hannahstratfull/physiological-monitoring/CAD/handheld device/!!__83.SLDPRT

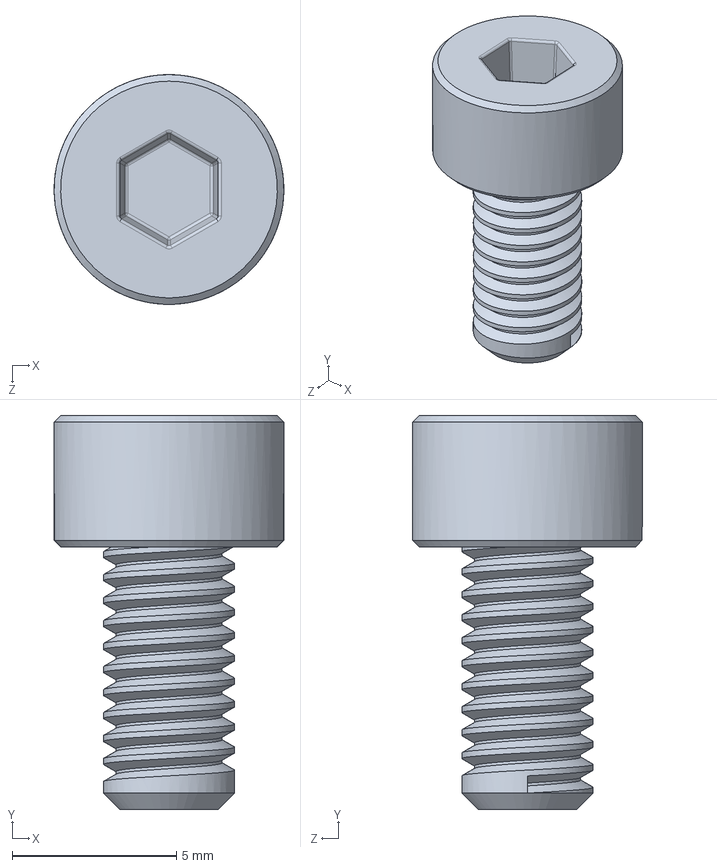
[picture p15: CAD file, 2022-05-07]
CAD/handheld device/!!__83.SLDPRT
7.00 x 12.0 x 7.00 mm
