hannahstratfull/physiological-monitoring/CAD/LCD/Back Plate.SLDPRT

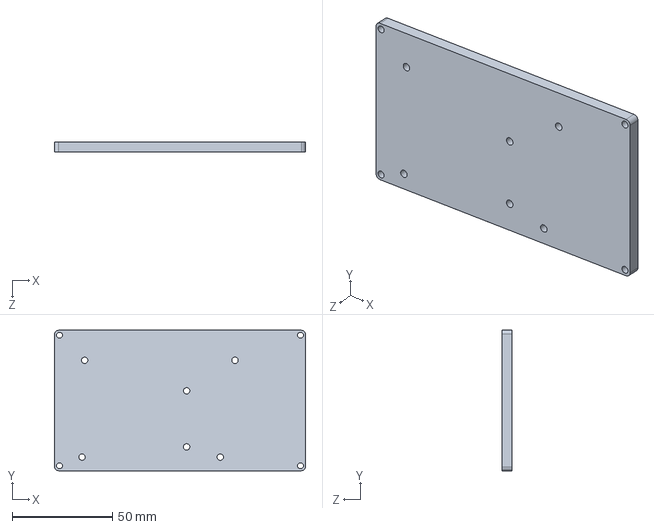
[picture p16: CAD file, 2022-05-07]
CAD/LCD/Back Plate.SLDPRT
125.0 x 70.0 x 5.00 mm
