hannahstratfull/physiological-monitoring/CAD/microphone/Name tag.SLDPRT

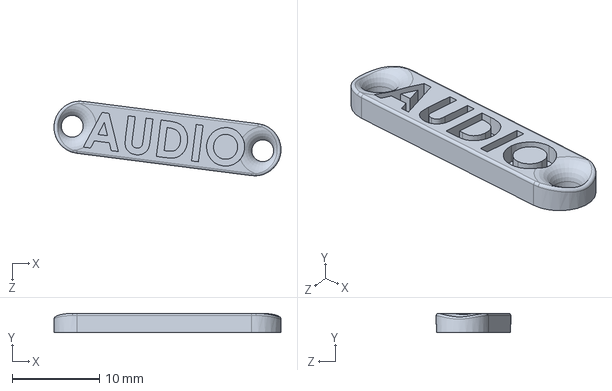
[picture p17: CAD file, 2022-05-07]
CAD/microphone/Name tag.SLDPRT
26.0 x 2.20 x 8.56 mm
