hannahstratfull/physiological-monitoring/CAD/ECG/ECG module.SLDPRT

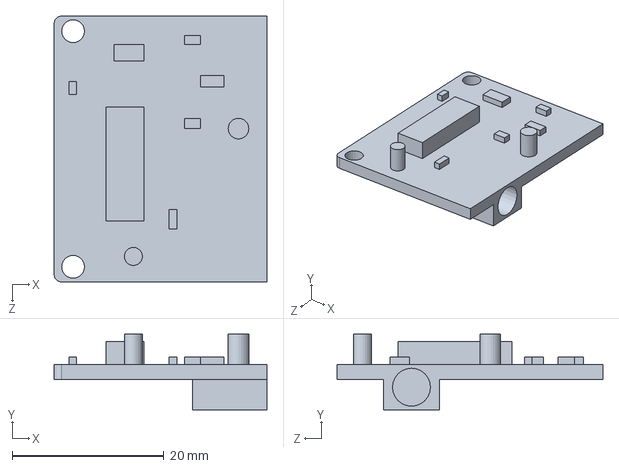
[picture p18: CAD file, 2022-05-07]
CAD/ECG/ECG module.SLDPRT
28.0 x 10.0 x 35.0 mm
