hannahstratfull/physiological-monitoring/CAD/EMG/Name tag.SLDPRT

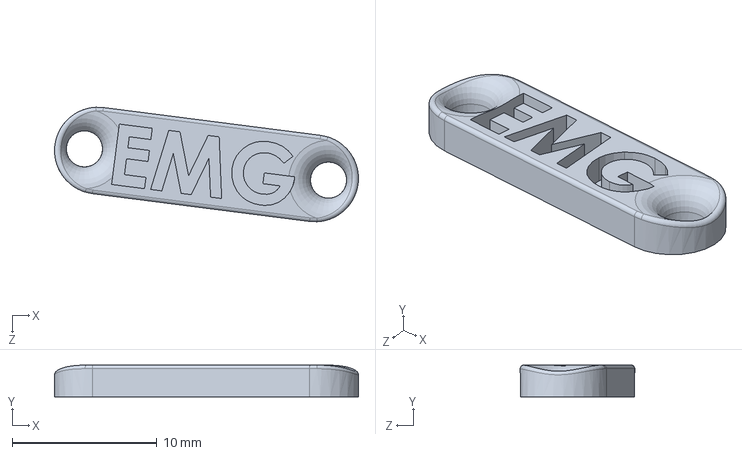
[picture p19: CAD file, 2022-05-07]
CAD/EMG/Name tag.SLDPRT
21.0 x 2.20 x 7.91 mm
