hannahstratfull/physiological-monitoring/CAD/LCD/LED 5mm.SLDPRT

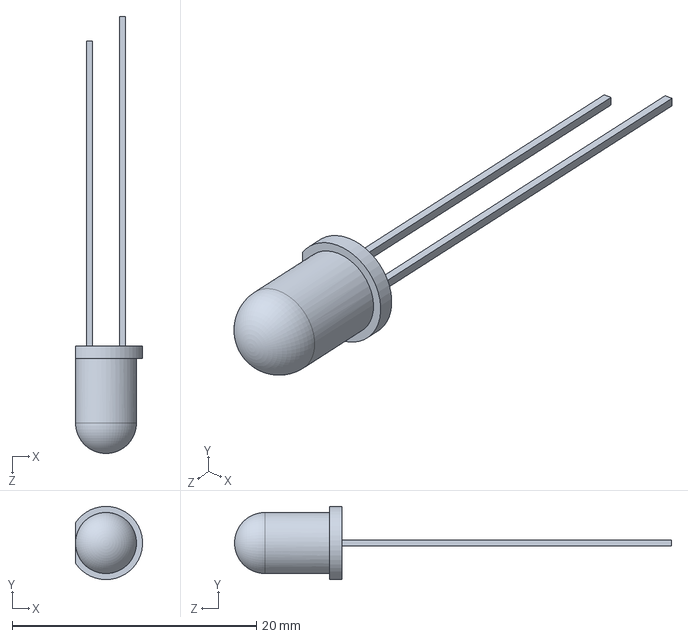
[picture p20: CAD file, 2022-05-07]
CAD/LCD/LED 5mm.SLDPRT
5.49 x 6.00 x 35.8 mm
