hannahstratfull/physiological-monitoring/CAD/microphone/Microphone Lid.SLDPRT

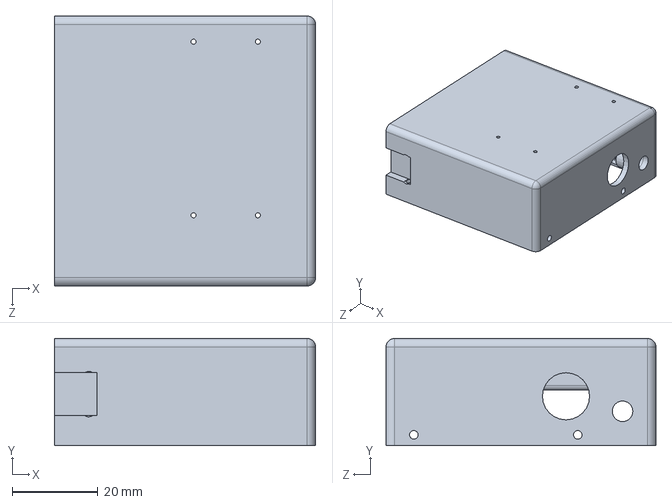
[picture p21: CAD file, 2022-05-07]
CAD/microphone/Microphone Lid.SLDPRT
61.0 x 25.0 x 63.0 mm
