hannahstratfull/physiological-monitoring/CAD/ECG/ECG Box Lid.SLDPRT

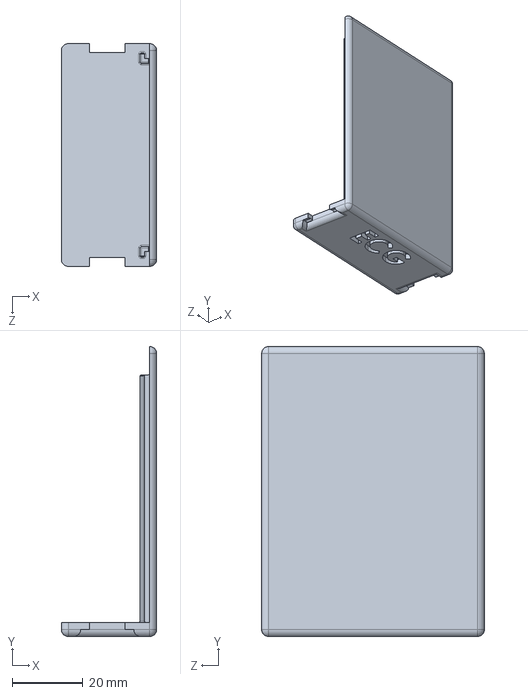
[picture p22: CAD file, 2022-05-07]
CAD/ECG/ECG Box Lid.SLDPRT
27.0 x 82.0 x 63.0 mm
