hannahstratfull/physiological-monitoring/CAD/EMG/EMG box.SLDPRT

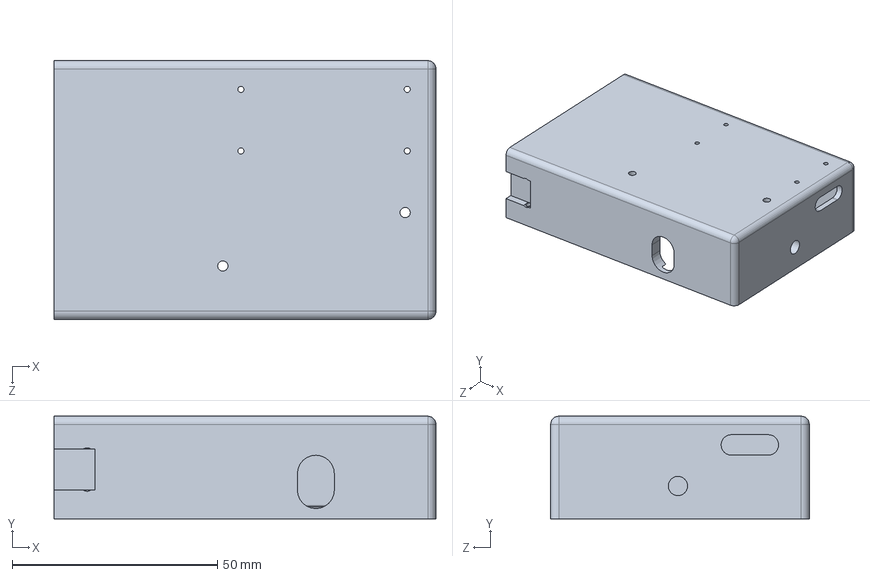
[picture p23: CAD file, 2022-05-07]
CAD/EMG/EMG box.SLDPRT
93.0 x 25.0 x 63.0 mm
