hannahstratfull/physiological-monitoring/CAD/Flexiforce/Flexiforce cable holder.SLDPRT

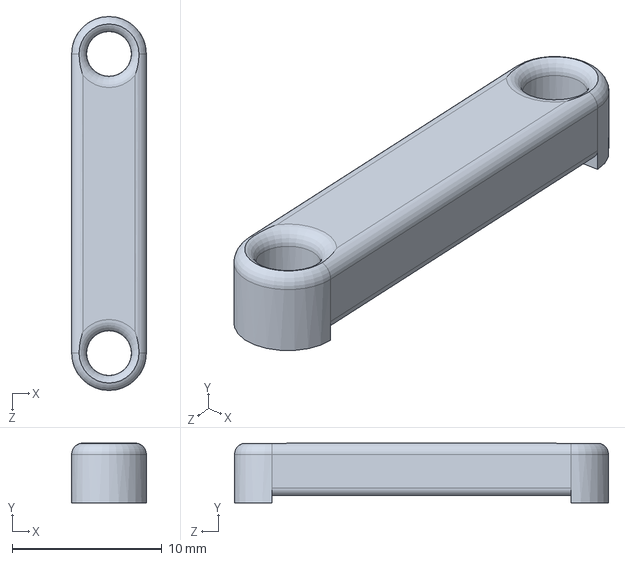
[picture p24: CAD file, 2022-05-07]
CAD/Flexiforce/Flexiforce cable holder.SLDPRT
5.00 x 4.00 x 25.0 mm
