hannahstratfull/physiological-monitoring/CAD/ECG/Name tag.SLDPRT

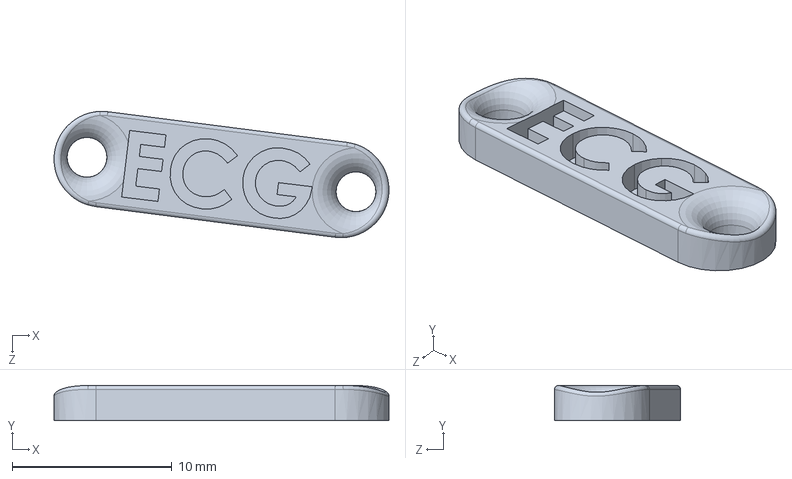
[picture p25: CAD file, 2022-05-07]
CAD/ECG/Name tag.SLDPRT
21.0 x 2.20 x 7.91 mm
