hannahstratfull/physiological-monitoring/CAD/Flexiforce/button top.SLDPRT

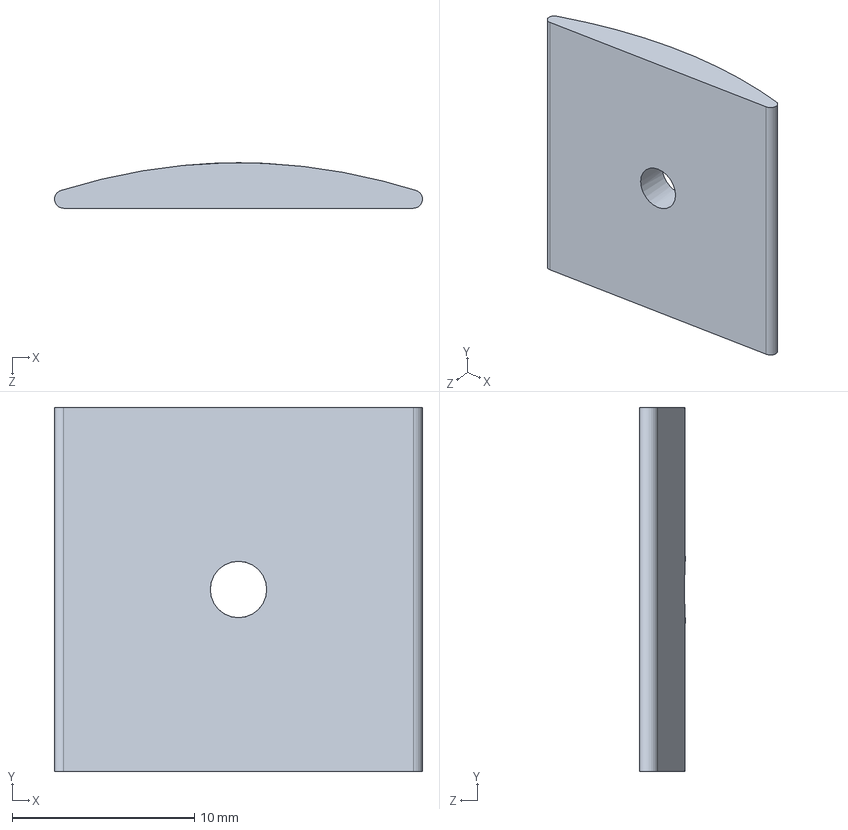
[picture p26: CAD file, 2022-05-07]
CAD/Flexiforce/button top.SLDPRT
20.2 x 20.0 x 2.50 mm
