hannahstratfull/physiological-monitoring/CAD/handheld device/rocker switch 1.SLDPRT

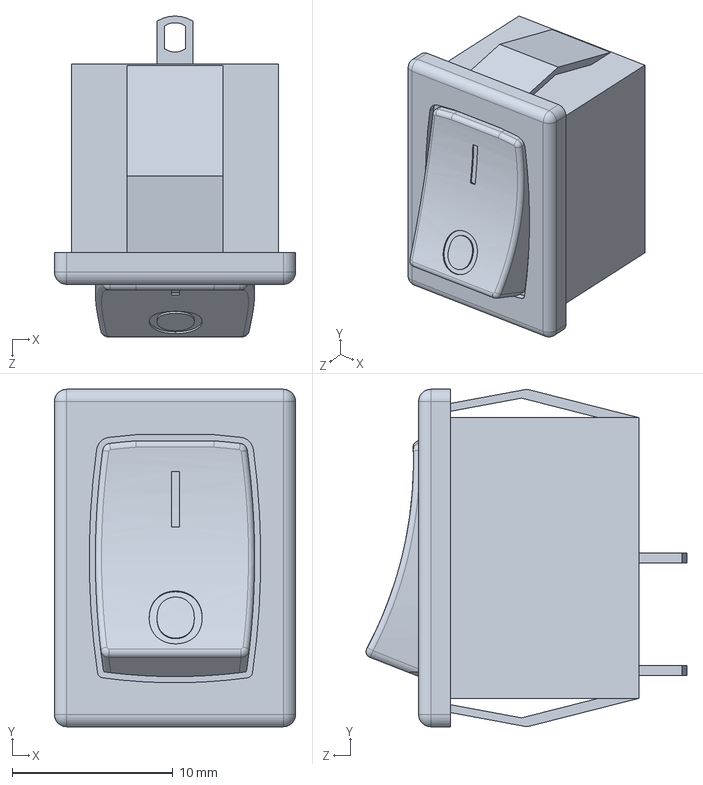
[picture p27: CAD file, 2022-05-07]
CAD/handheld device/rocker switch 1.SLDPRT
15.0 x 21.0 x 20.0 mm
