hannahstratfull/physiological-monitoring/CAD/LCD/Box.SLDPRT

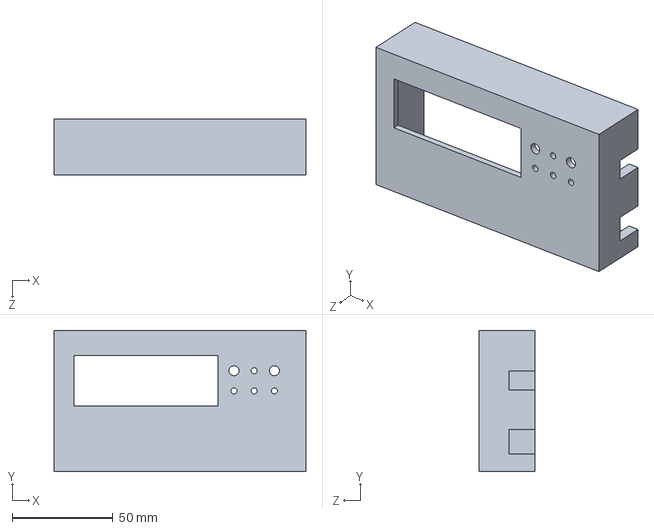
[picture p28: CAD file, 2022-05-07]
CAD/LCD/Box.SLDPRT
125.0 x 70.0 x 28.0 mm
