hannahstratfull/physiological-monitoring/CAD/microphone/audio module.SLDPRT

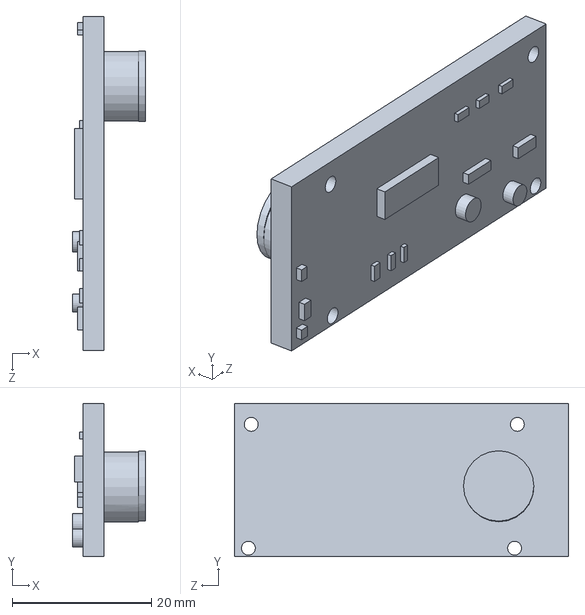
[picture p29: CAD file, 2022-05-07]
CAD/microphone/audio module.SLDPRT
10.5 x 22.0 x 48.0 mm
