hannahstratfull/physiological-monitoring/CAD/ECG/Spacer.SLDPRT

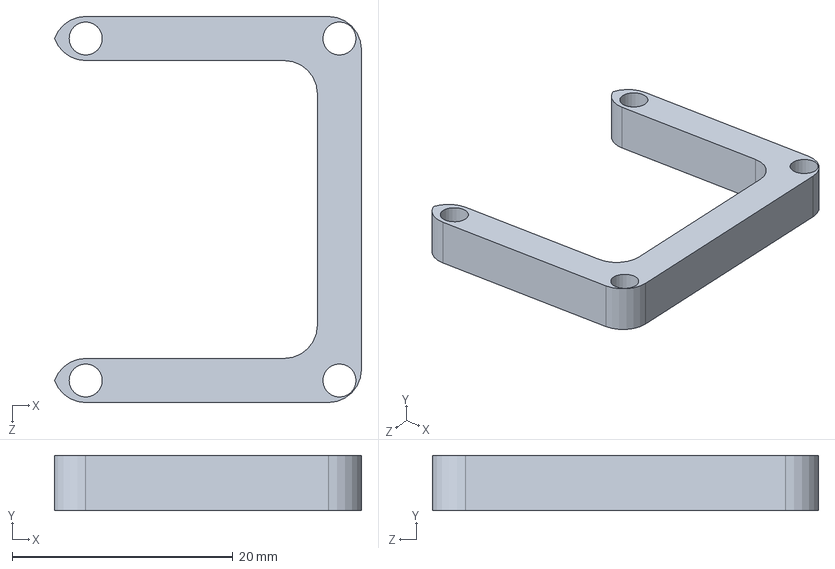
[picture p30: CAD file, 2022-05-07]
CAD/ECG/Spacer.SLDPRT
27.8 x 5.00 x 35.0 mm
