hannahstratfull/physiological-monitoring/CAD/EMG/EMG Box Lid mk2.STL

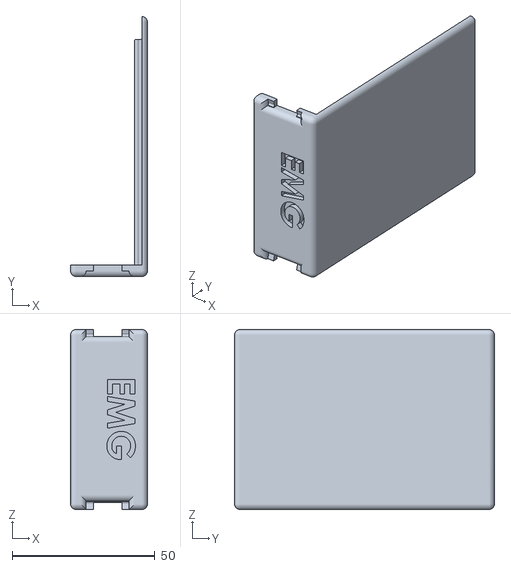
[picture p31: CAD file, 2022-05-07]
CAD/EMG/EMG Box Lid mk2.STL
27.0 x 91.0 x 63.0
