hannahstratfull/physiological-monitoring/CAD/Flexiforce/Flexiforce flex lid bat sec.SLDPRT

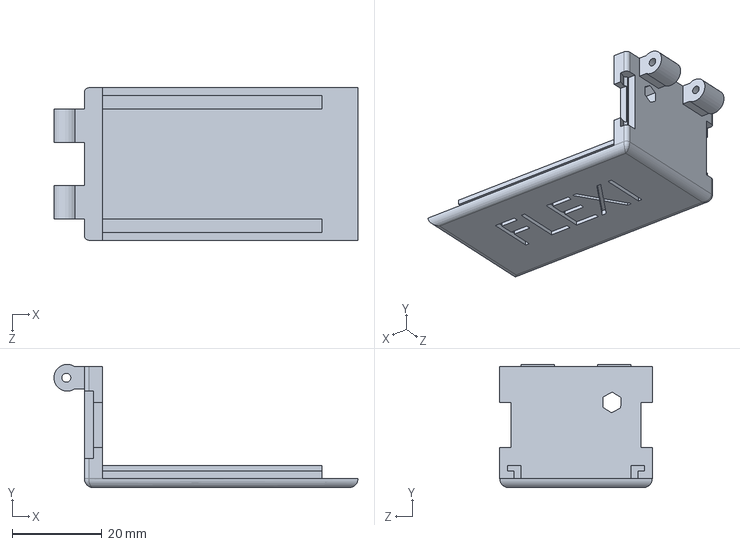
[picture p32: CAD file, 2022-05-07]
CAD/Flexiforce/Flexiforce flex lid bat sec.SLDPRT
67.8 x 27.5 x 34.0 mm
