hannahstratfull/physiological-monitoring/CAD/ECG/Spacer Short.SLDPRT

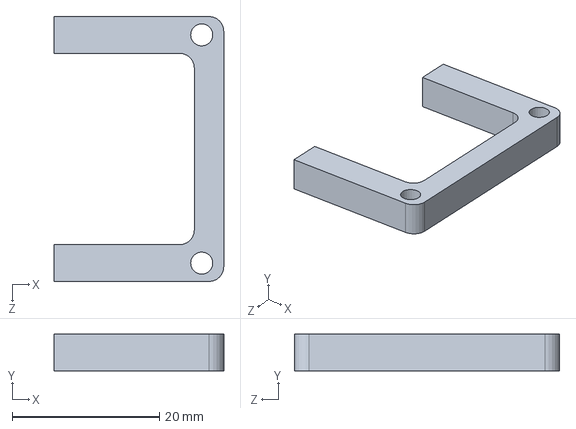
[picture p33: CAD file, 2022-05-07]
CAD/ECG/Spacer Short.SLDPRT
23.0 x 5.00 x 36.0 mm
