hannahstratfull/physiological-monitoring/CAD/EMG/Box Locking Part mk2.STL

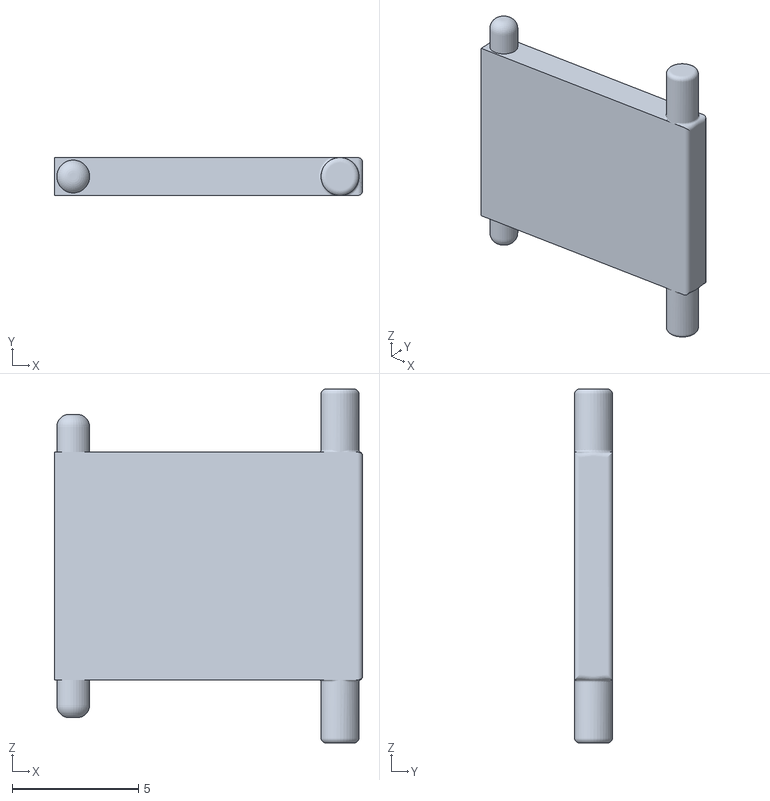
[picture p34: CAD file, 2022-05-07]
CAD/EMG/Box Locking Part mk2.STL
12.2 x 1.50 x 14.0
