hannahstratfull/physiological-monitoring/CAD/Flexiforce/Sensor compressive case with bottom.SLDPRT

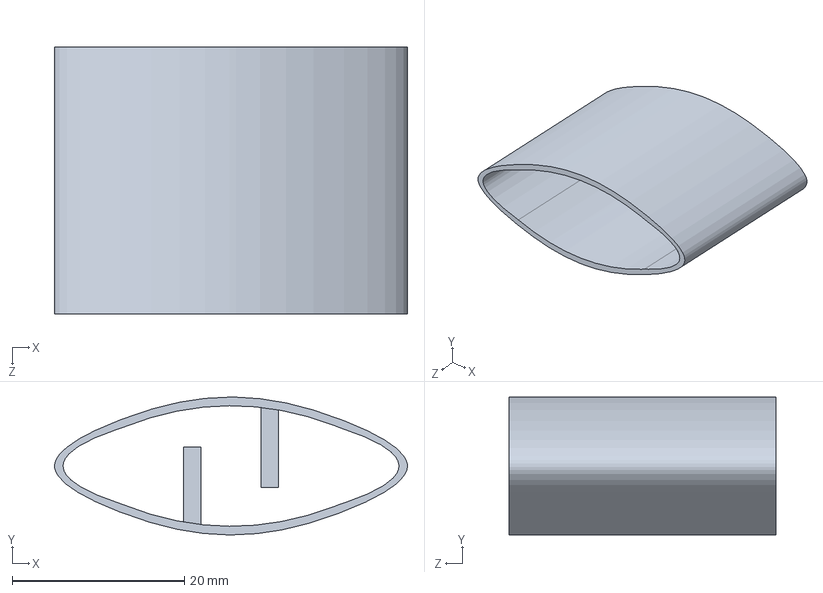
[picture p35: CAD file, 2022-05-07]
CAD/Flexiforce/Sensor compressive case with bottom.SLDPRT
41.0 x 16.0 x 31.0 mm
