hannahstratfull/physiological-monitoring/CAD/handheld device/M2.SLDPRT

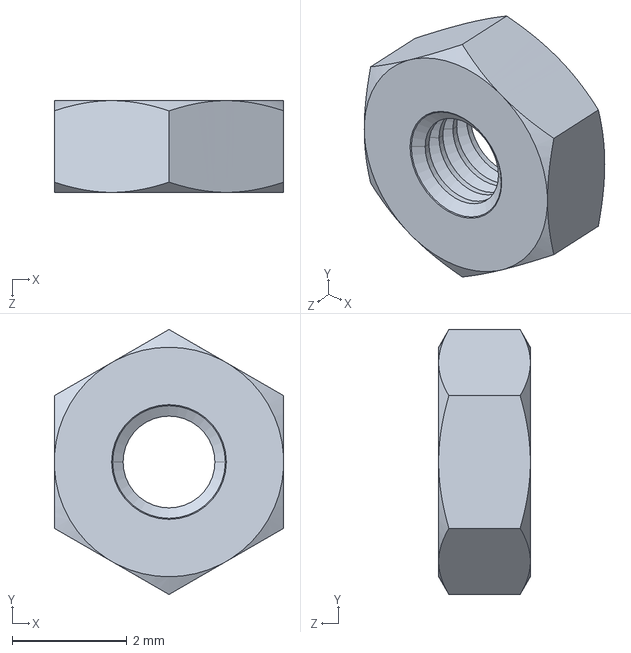
[picture p36: CAD file, 2022-05-07]
CAD/handheld device/M2.SLDPRT
4.00 x 4.62 x 1.60 mm
