hannahstratfull/physiological-monitoring/CAD/microphone/Microphone Box Lid.SLDPRT

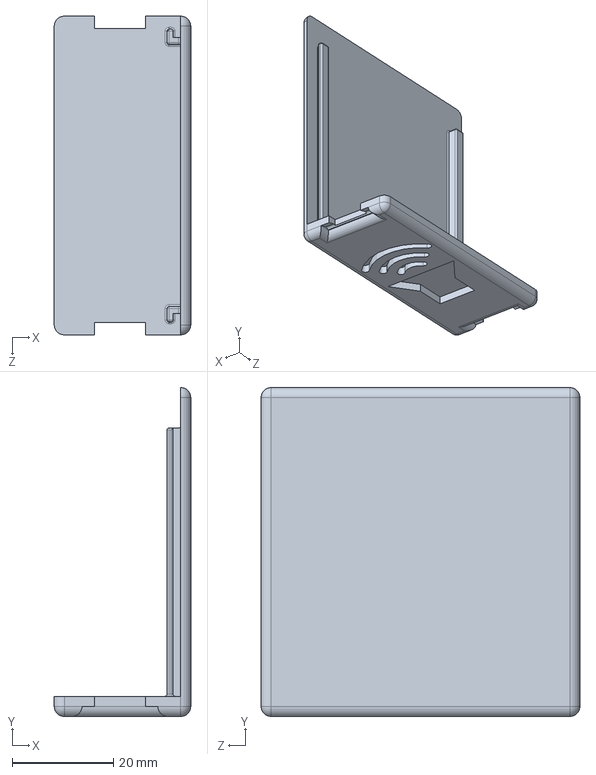
[picture p37: CAD file, 2022-05-07]
CAD/microphone/Microphone Box Lid.SLDPRT
27.0 x 65.0 x 63.0 mm
