hannahstratfull/physiological-monitoring/CAD/Flexiforce/Sensor holder upper right.SLDPRT

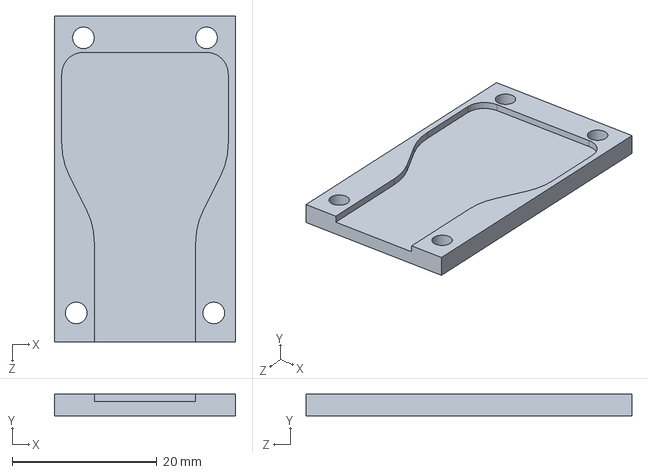
[picture p38: CAD file, 2022-05-07]
CAD/Flexiforce/Sensor holder upper right.SLDPRT
25.0 x 3.00 x 45.0 mm
