hannahstratfull/physiological-monitoring/CAD/microphone/myoware.step.SLDPRT

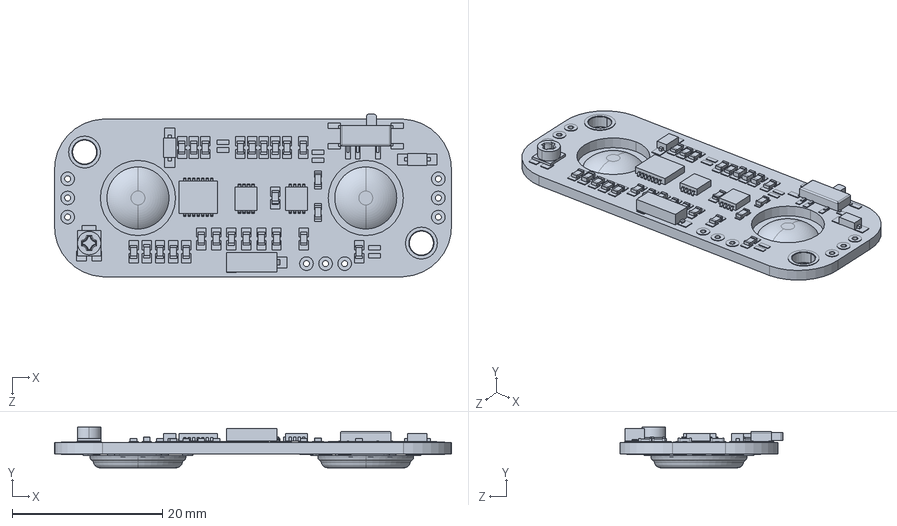
[picture p39: CAD file, 2022-05-07]
CAD/microphone/myoware.step.SLDPRT
52.8 x 5.42 x 21.6 mm
