hannahstratfull/physiological-monitoring/CAD/EMG/EMG Box Lid mk1.STL

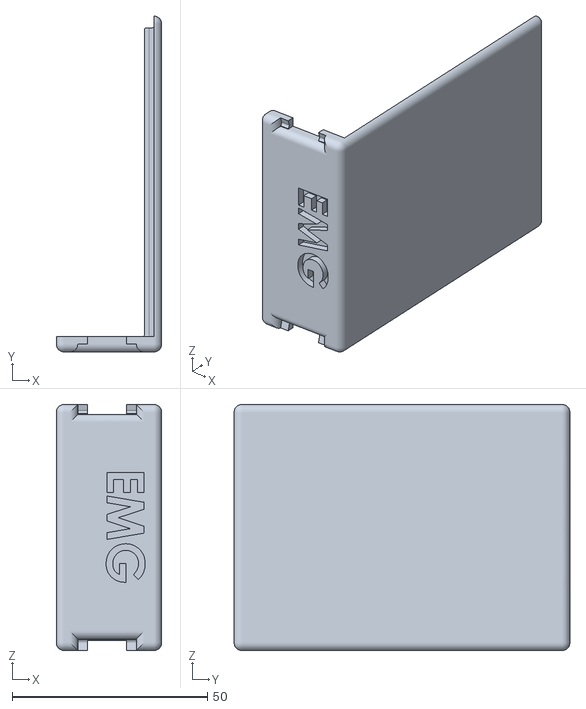
[picture p40: CAD file, 2022-05-07]
CAD/EMG/EMG Box Lid mk1.STL
27.0 x 86.0 x 63.0
