hannahstratfull/physiological-monitoring/CAD/Flexiforce/Flexi bend ard box.SLDPRT

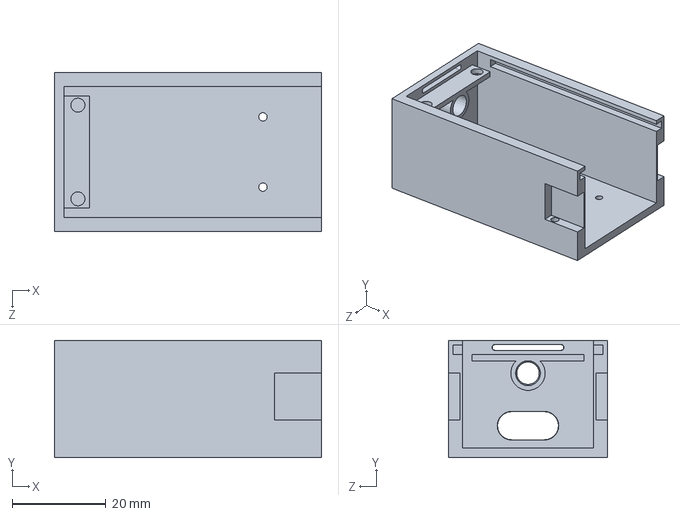
[picture p41: CAD file, 2022-05-07]
CAD/Flexiforce/Flexi bend ard box.SLDPRT
57.0 x 25.0 x 34.0 mm
