hannahstratfull/physiological-monitoring/CAD/microphone/9V-battery.SLDPRT

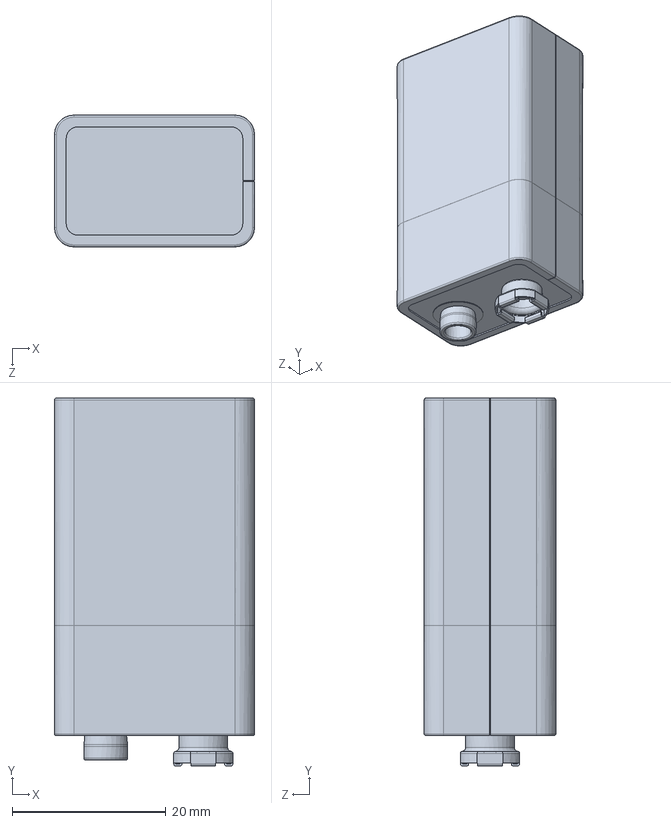
[picture p42: CAD file, 2022-05-07]
CAD/microphone/9V-battery.SLDPRT
26.0 x 47.9 x 17.1 mm
