hannahstratfull/physiological-monitoring/CAD/EMG/EMG box mk1.STL

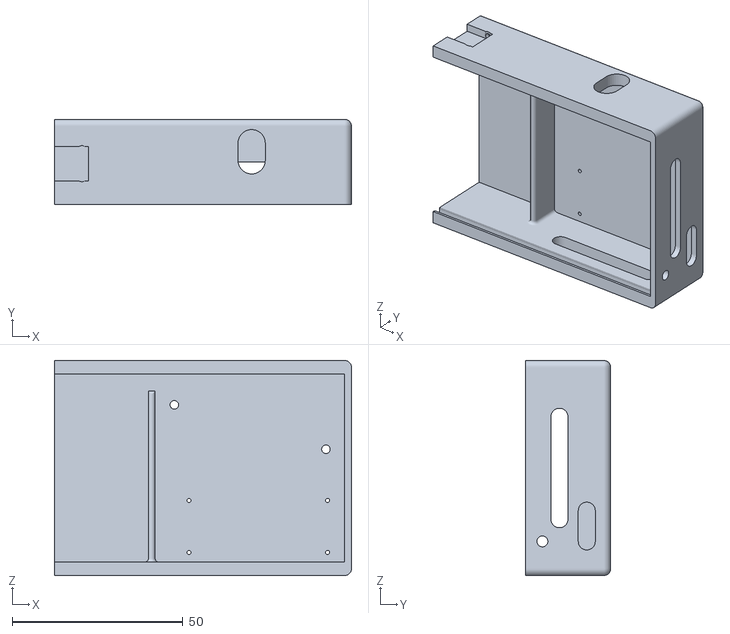
[picture p43: CAD file, 2022-05-07]
CAD/EMG/EMG box mk1.STL
87.0 x 25.0 x 63.0
