hannahstratfull/physiological-monitoring/CAD/Flexiforce/Cable compressor.SLDPRT

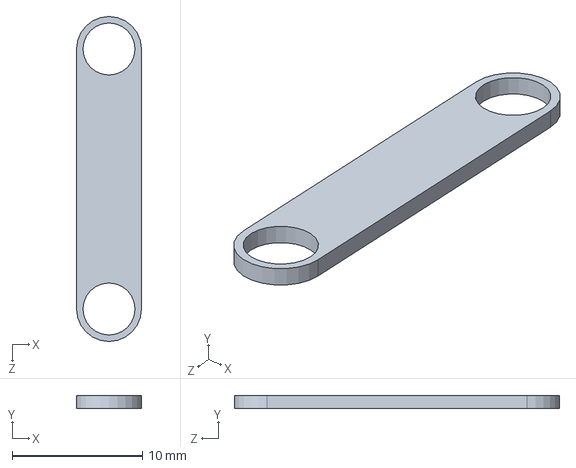
[picture p44: CAD file, 2022-05-07]
CAD/Flexiforce/Cable compressor.SLDPRT
5.00 x 1.00 x 25.0 mm
