hannahstratfull/physiological-monitoring/CAD/handheld device/Belt clip.SLDPRT

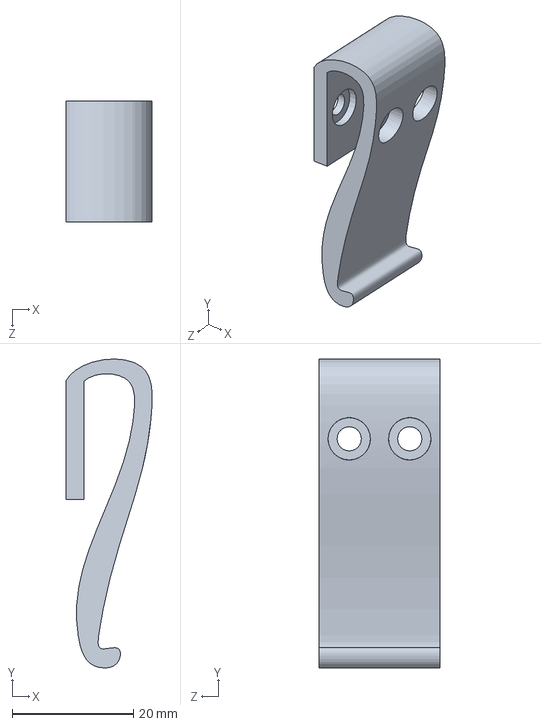
[picture p45: CAD file, 2022-05-07]
CAD/handheld device/Belt clip.SLDPRT
14.3 x 51.0 x 20.0 mm
