hannahstratfull/physiological-monitoring/CAD/EMG/CE3E3_Spacer mk1.3mf

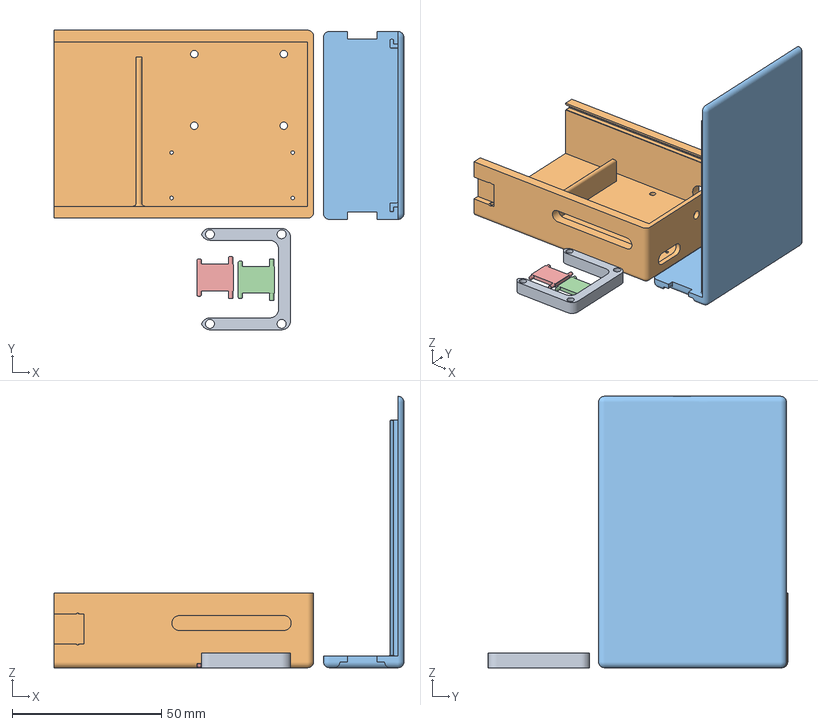
[picture p46: CAD file, 2022-05-07]
CAD/EMG/CE3E3_Spacer mk1.3mf
117.3 x 100.4 x 91.0 mm
Spacer mk1.STL
ECG box mk1.STL
ECG Box Lid mk1.STL
Box Locking Part.STL
Box Locking Part.STL(1)
