hannahstratfull/physiological-monitoring/CAD/Flexiforce/Flexiforce hoop.SLDPRT

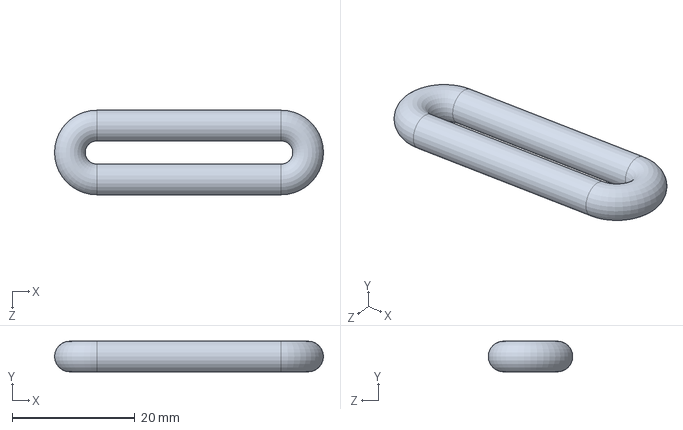
[picture p47: CAD file, 2022-05-07]
CAD/Flexiforce/Flexiforce hoop.SLDPRT
43.8 x 5.00 x 13.8 mm
