hannahstratfull/physiological-monitoring/CAD/EMG/Box Locking Part.STL

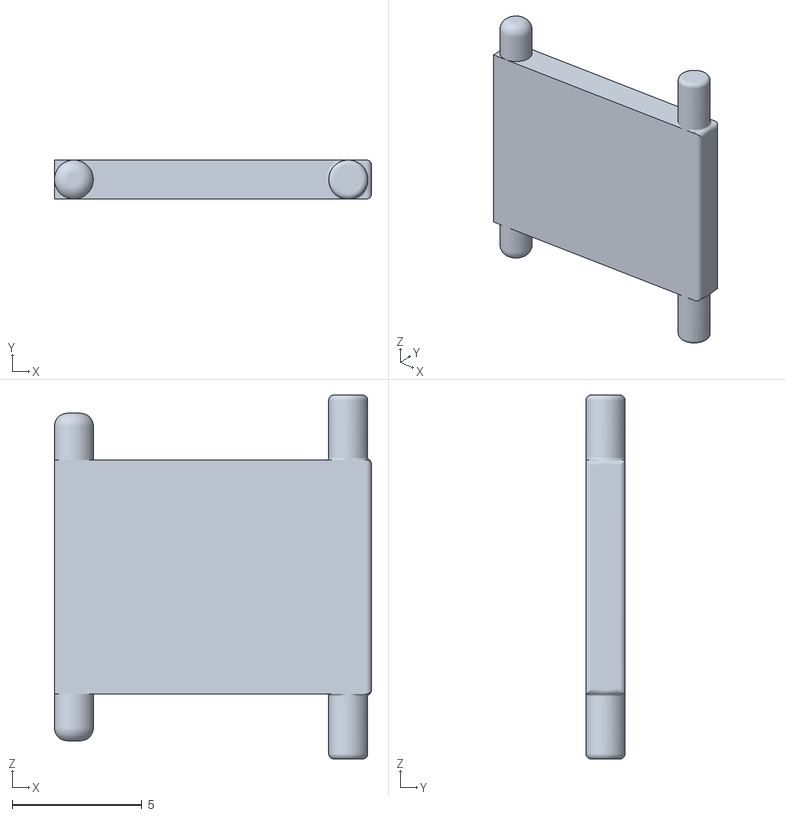
[picture p48: CAD file, 2022-05-07]
CAD/EMG/Box Locking Part.STL
12.2 x 1.50 x 14.0
