hannahstratfull/physiological-monitoring/CAD/Flexiforce/Sensor holder part 1.SLDPRT

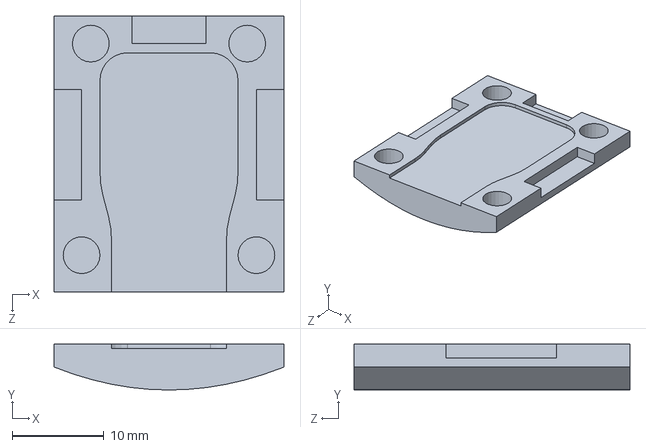
[picture p49: CAD file, 2022-05-07]
CAD/Flexiforce/Sensor holder part 1.SLDPRT
25.0 x 5.00 x 30.0 mm
