hannahstratfull/physiological-monitoring/CAD/Flexiforce/Strap holders.SLDPRT

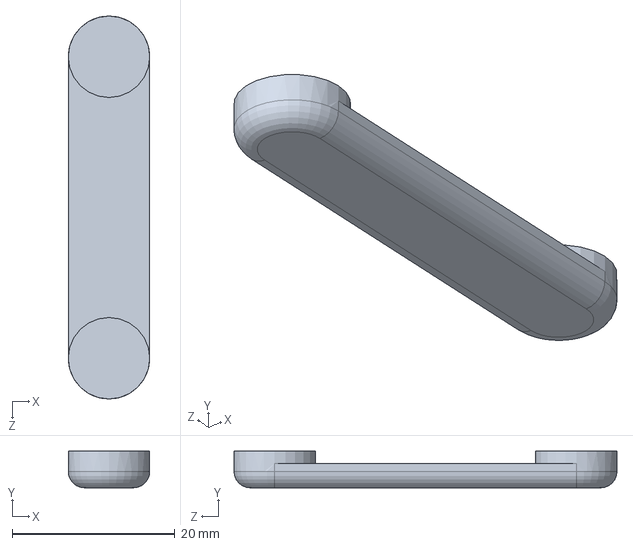
[picture p50: CAD file, 2022-05-07]
CAD/Flexiforce/Strap holders.SLDPRT
10.0 x 4.50 x 47.0 mm
