hannahstratfull/physiological-monitoring/CAD/ECG/Spacer mk1.STL

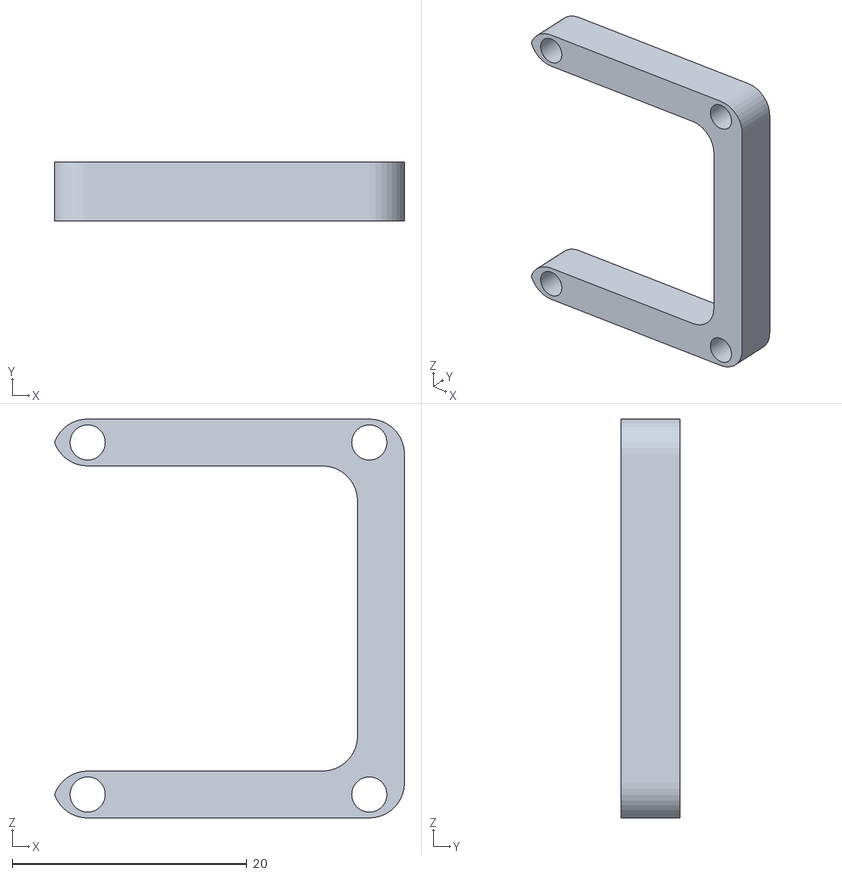
[picture p51: CAD file, 2022-05-07]
CAD/ECG/Spacer mk1.STL
29.8 x 5.00 x 34.0
