hannahstratfull/physiological-monitoring/CAD/Flexiforce/Flexi belt hoop final.SLDPRT

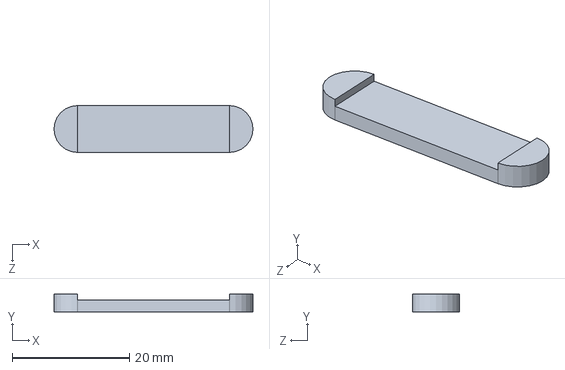
[picture p52: CAD file, 2022-05-07]
CAD/Flexiforce/Flexi belt hoop final.SLDPRT
34.0 x 3.00 x 8.00 mm
