hannahstratfull/physiological-monitoring/CAD/Flexiforce/Flexiforce flex lid arduino sec.SLDPRT

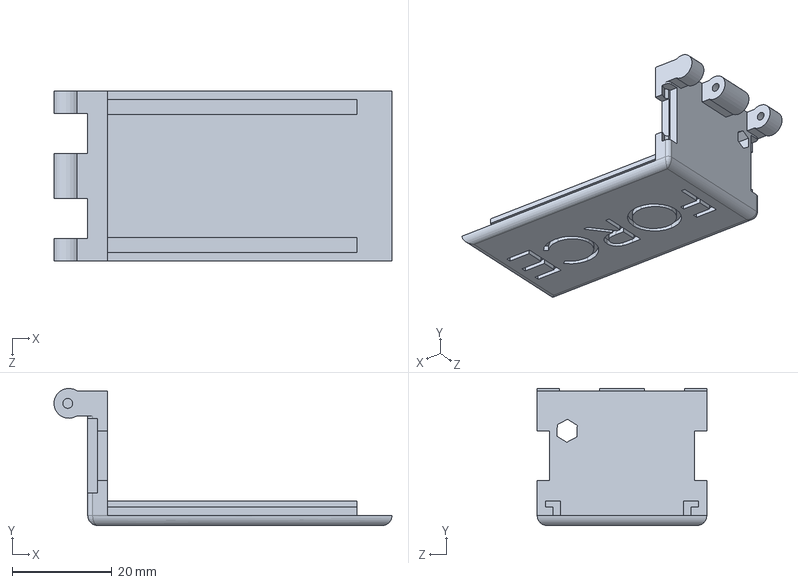
[picture p53: CAD file, 2022-05-07]
CAD/Flexiforce/Flexiforce flex lid arduino sec.SLDPRT
67.8 x 27.5 x 34.0 mm
