hannahstratfull/physiological-monitoring/CAD/Flexiforce/Button smaller dimentions.SLDPRT

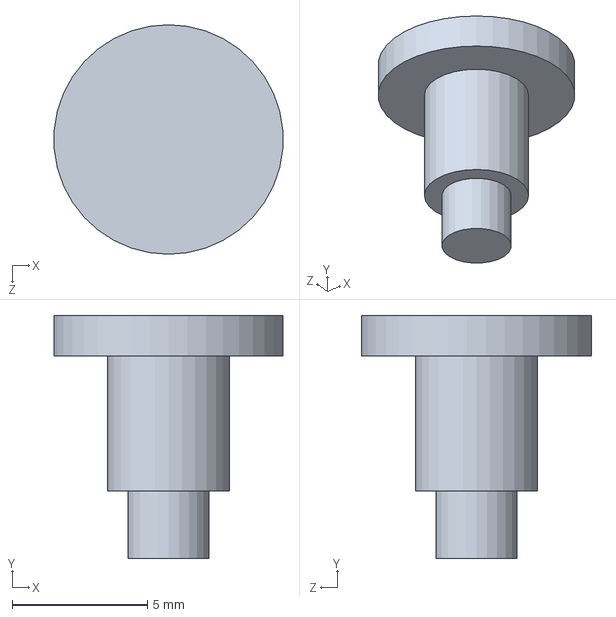
[picture p54: CAD file, 2022-05-07]
CAD/Flexiforce/Button smaller dimentions.SLDPRT
8.47 x 9.00 x 8.50 mm
