hannahstratfull/physiological-monitoring/CAD/Flexiforce/Sensor holder upper 30mm mk2.STL

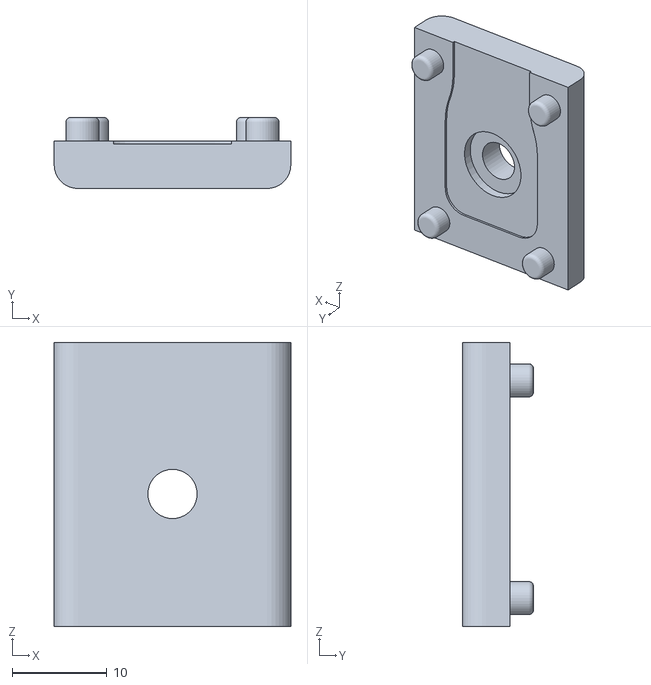
[picture p55: CAD file, 2022-05-07]
CAD/Flexiforce/Sensor holder upper 30mm mk2.STL
25.0 x 7.50 x 30.0
