hannahstratfull/physiological-monitoring/CAD/Flexiforce/Sensor compressive case with bottom mk3.STL

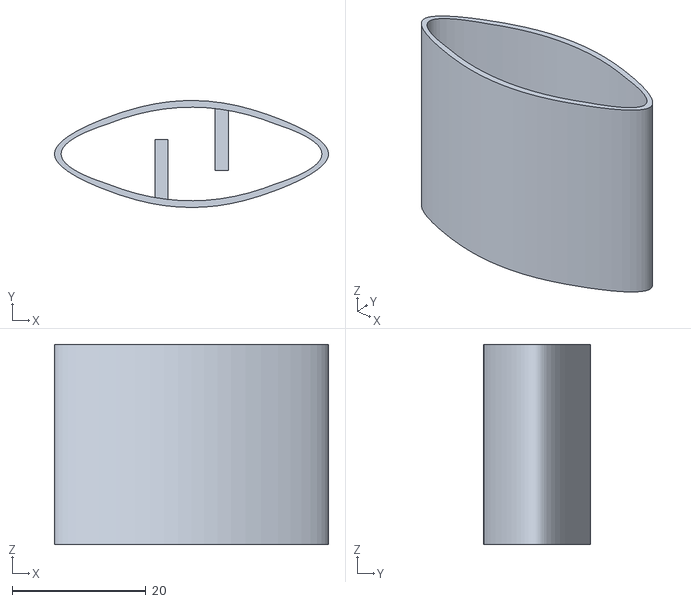
[picture p56: CAD file, 2022-05-07]
CAD/Flexiforce/Sensor compressive case with bottom mk3.STL
41.0 x 16.0 x 30.0
