hannahstratfull/physiological-monitoring/CAD/Flexiforce/Sensor compressive case for 3d print.STL

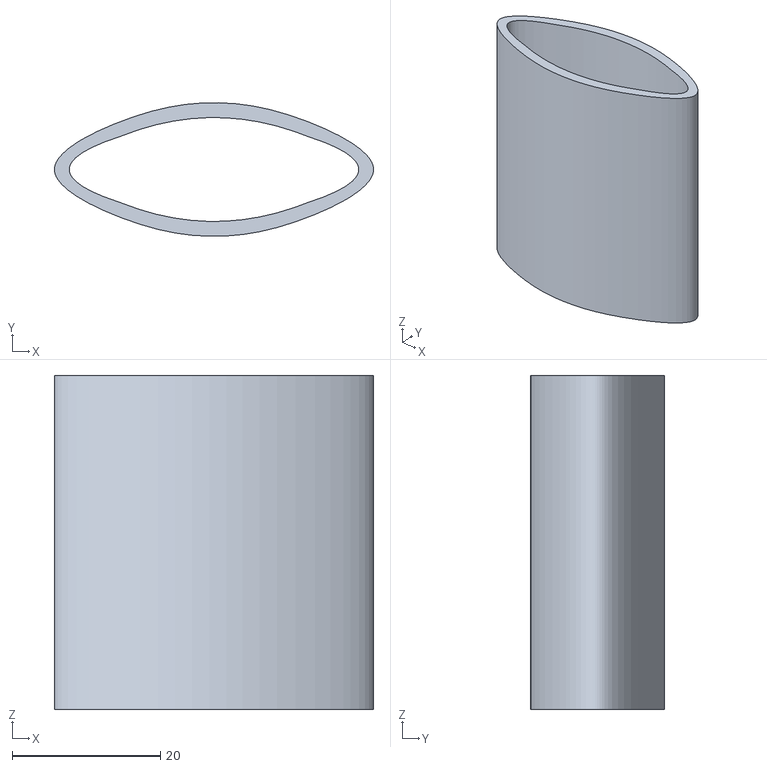
[picture p57: CAD file, 2022-05-07]
CAD/Flexiforce/Sensor compressive case for 3d print.STL
43.0 x 18.0 x 45.0
