hannahstratfull/physiological-monitoring/CAD/Flexiforce/Flexiforce hoop - half mk3.STL

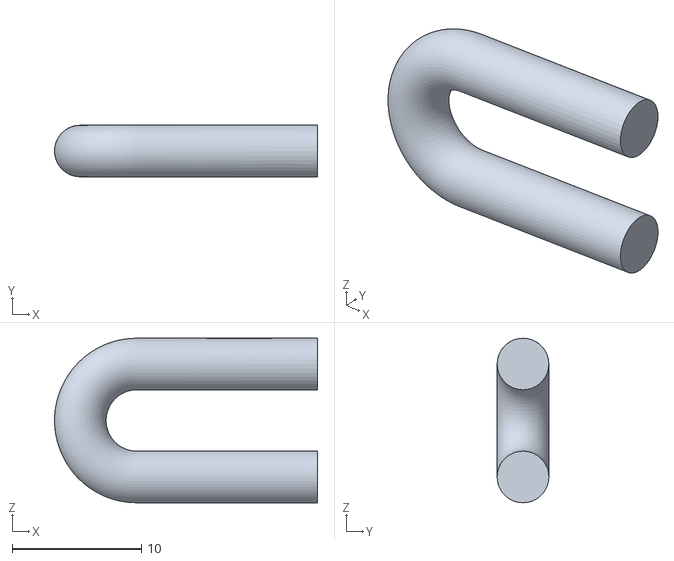
[picture p58: CAD file, 2022-05-07]
CAD/Flexiforce/Flexiforce hoop - half mk3.STL
20.4 x 4.00 x 12.7
