hannahstratfull/physiological-monitoring/CAD/Flexiforce/Felxiforce case with hoop - Flexiforce hoop-1.STL

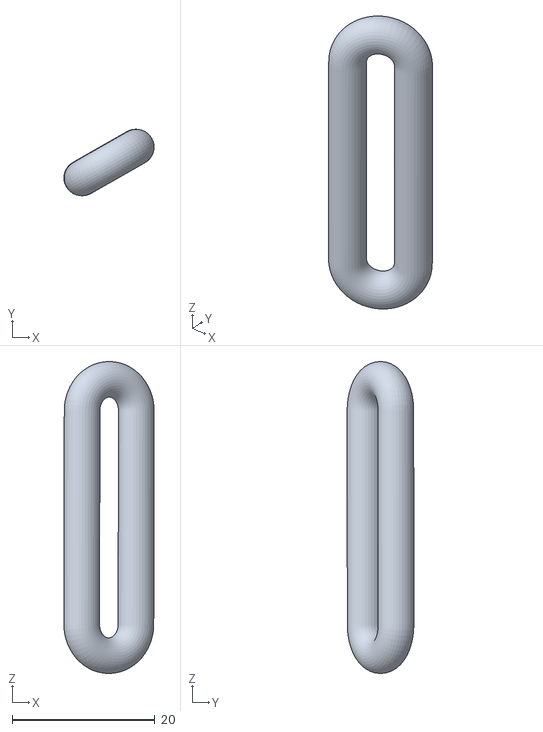
[picture p59: CAD file, 2022-05-07]
CAD/Flexiforce/Felxiforce case with hoop - Flexiforce hoop-1.STL
12.7 x 9.35 x 43.7
