hannahstratfull/physiological-monitoring/CAD/Flexiforce/Felxiforce case with hoop - Sensor compressive case with bottom-1.STL

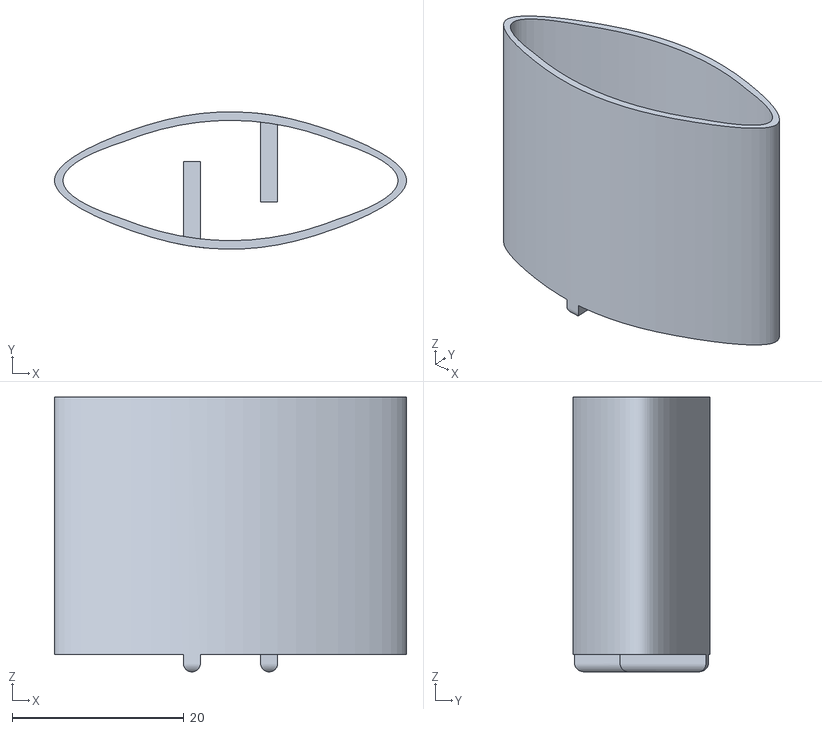
[picture p60: CAD file, 2022-05-07]
CAD/Flexiforce/Felxiforce case with hoop - Sensor compressive case with bottom-1.STL
41.0 x 16.0 x 32.0
