hannahstratfull/physiological-monitoring/CAD/Flexiforce/Flexiforce flex lid bat sec final mk4.STL

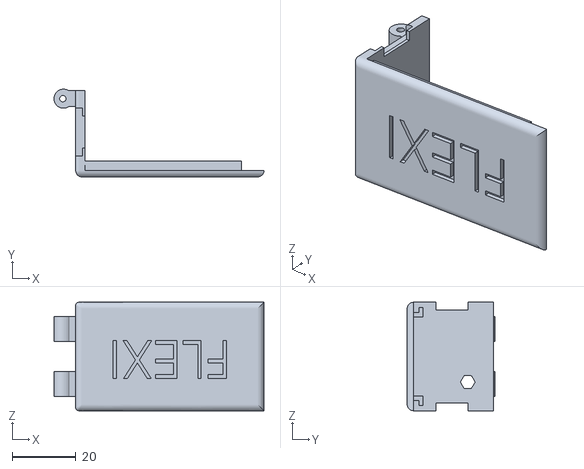
[picture p61: CAD file, 2022-05-07]
CAD/Flexiforce/Flexiforce flex lid bat sec final mk4.STL
65.8 x 27.5 x 34.0
