hannahstratfull/physiological-monitoring/CAD/Flexiforce/Button 3d print 3.STL

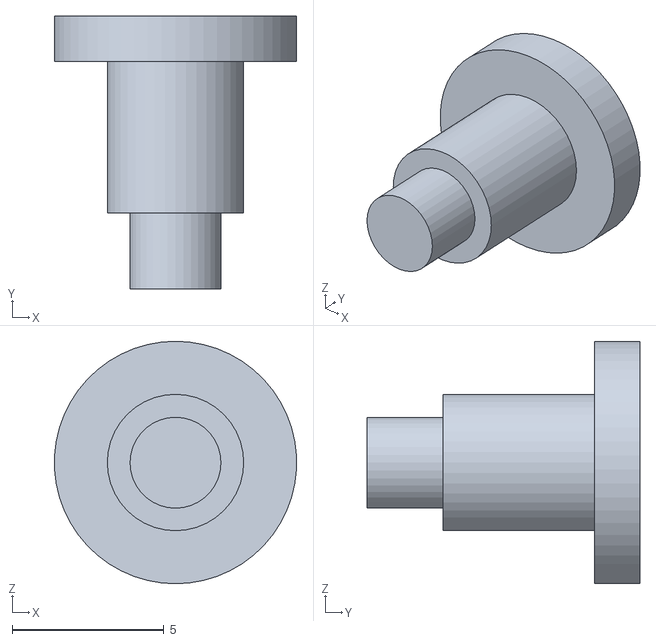
[picture p62: CAD file, 2022-05-07]
CAD/Flexiforce/Button 3d print 3.STL
7.99 x 9.00 x 8.00
