hannahstratfull/physiological-monitoring/CAD/Flexiforce/Flexiforce flex lid arduino sec MK1.STL

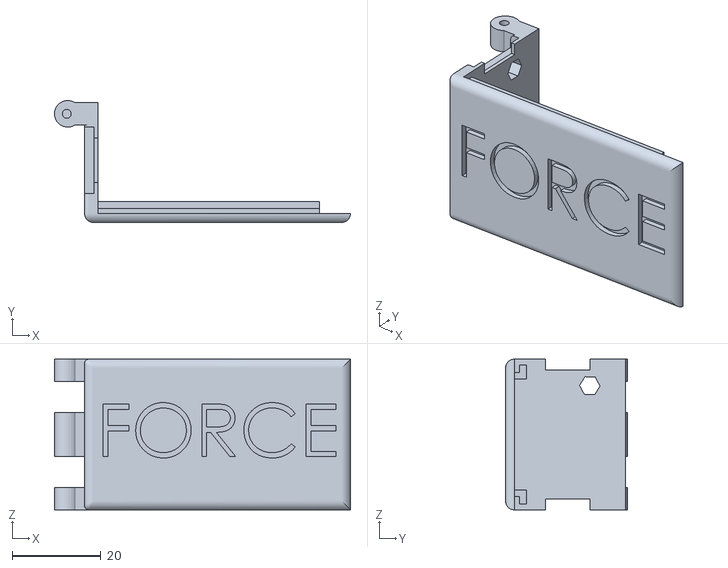
[picture p63: CAD file, 2022-05-07]
CAD/Flexiforce/Flexiforce flex lid arduino sec MK1.STL
66.8 x 27.5 x 34.0
