hannahstratfull/physiological-monitoring/CAD/Flexiforce/Box Locking Part mk1.STL

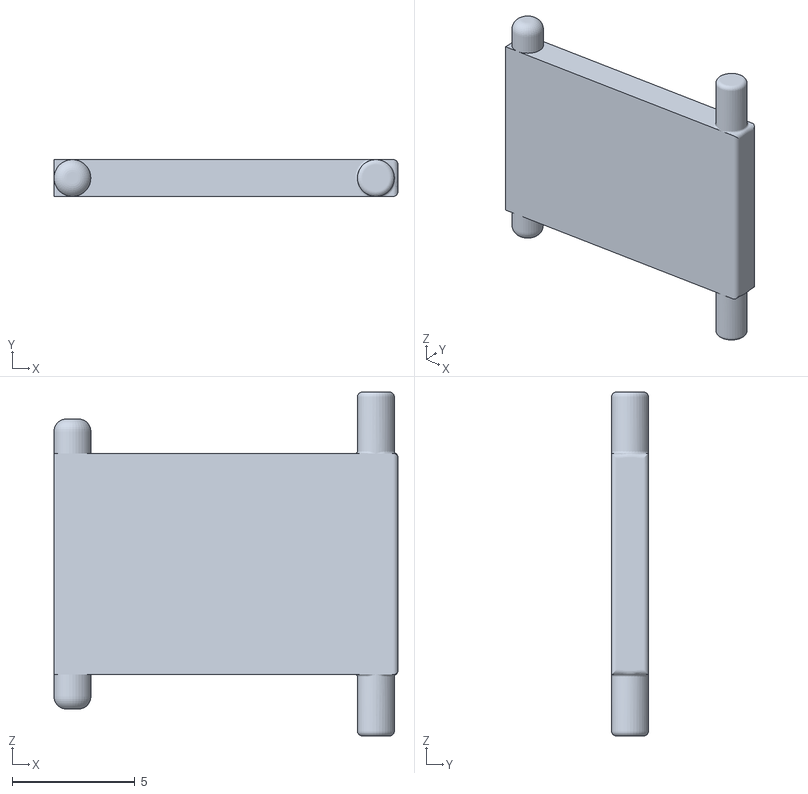
[picture p64: CAD file, 2022-05-07]
CAD/Flexiforce/Box Locking Part mk1.STL
14.0 x 1.50 x 14.0
