hannahstratfull/physiological-monitoring/CAD/Flexiforce/Flexiforce hoop - half final mk1.STL

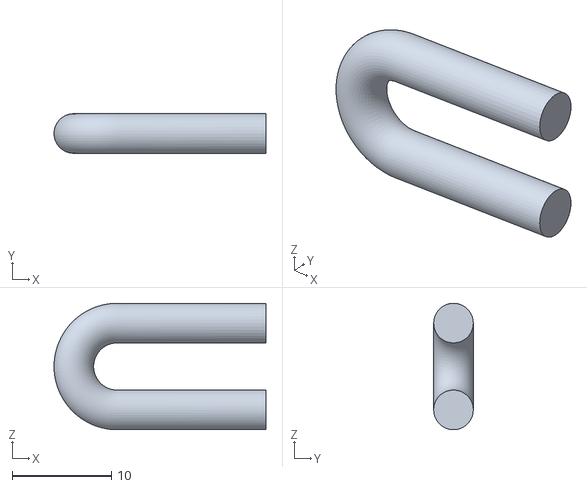
[picture p65: CAD file, 2022-05-07]
CAD/Flexiforce/Flexiforce hoop - half final mk1.STL
21.4 x 4.00 x 12.8
