hannahstratfull/physiological-monitoring/CAD/Flexiforce/Felxiforce case with hoop mk2 - Flexiforce hoop-2.STL

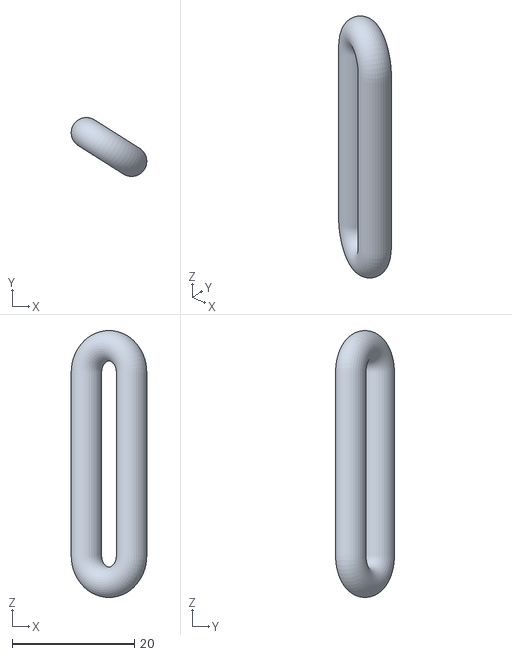
[picture p66: CAD file, 2022-05-07]
CAD/Flexiforce/Felxiforce case with hoop mk2 - Flexiforce hoop-2.STL
12.4 x 9.66 x 43.7
