hannahstratfull/physiological-monitoring/CAD/Flexiforce/Flexiforce box v2.STL

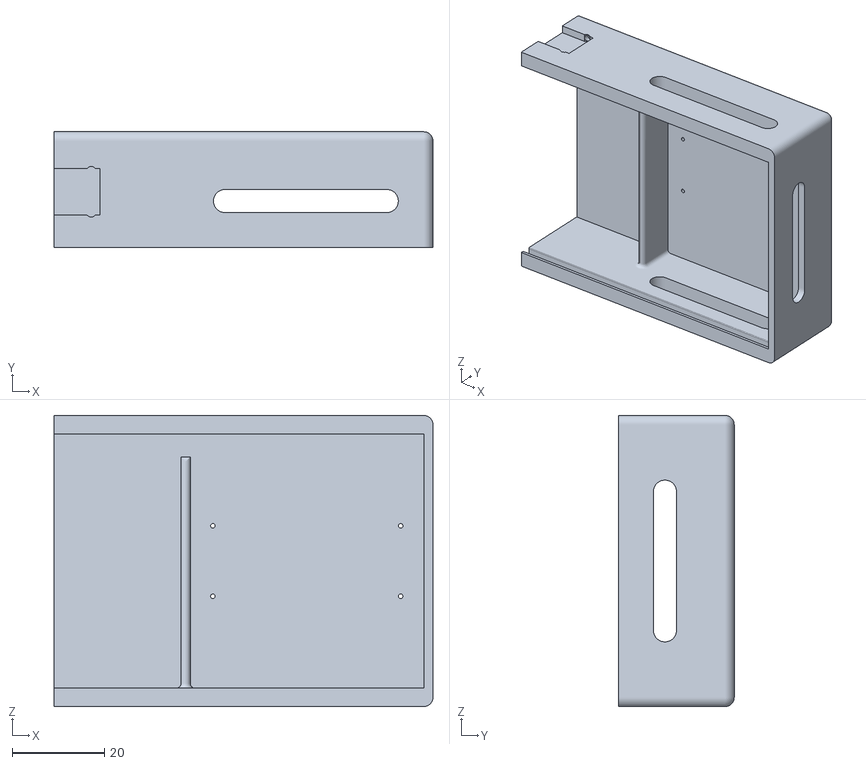
[picture p67: CAD file, 2022-05-07]
CAD/Flexiforce/Flexiforce box v2.STL
82.0 x 25.0 x 63.0
