hannahstratfull/physiological-monitoring/CAD/Flexiforce/Sensor holder upper for 3d print.STL

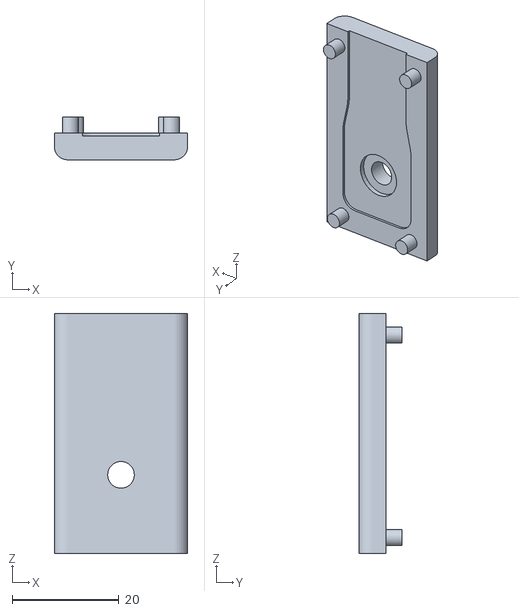
[picture p68: CAD file, 2022-05-07]
CAD/Flexiforce/Sensor holder upper for 3d print.STL
25.0 x 8.00 x 45.0
