hannahstratfull/physiological-monitoring/CAD/Flexiforce/Sensor compressive case thin for 3d print.STL

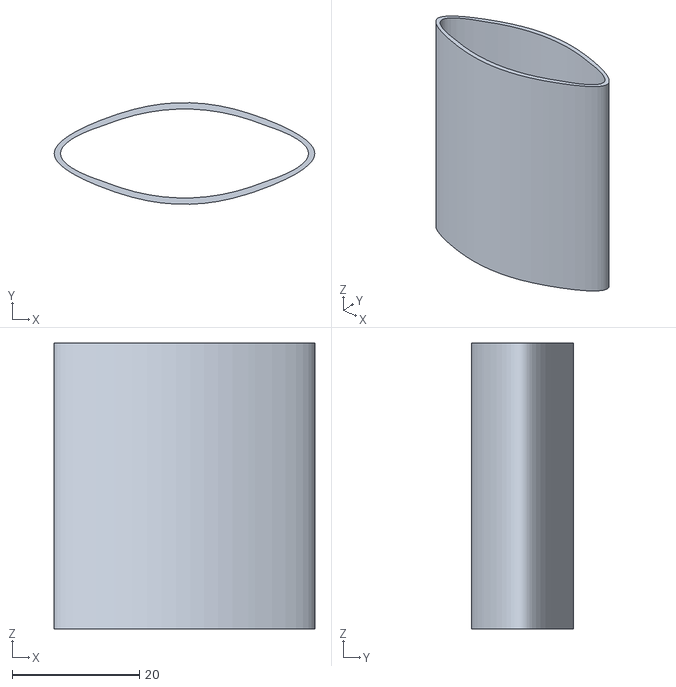
[picture p69: CAD file, 2022-05-07]
CAD/Flexiforce/Sensor compressive case thin for 3d print.STL
41.0 x 16.0 x 45.0
