hannahstratfull/physiological-monitoring/CAD/Flexiforce/Sensor holder upper 30mm.STL

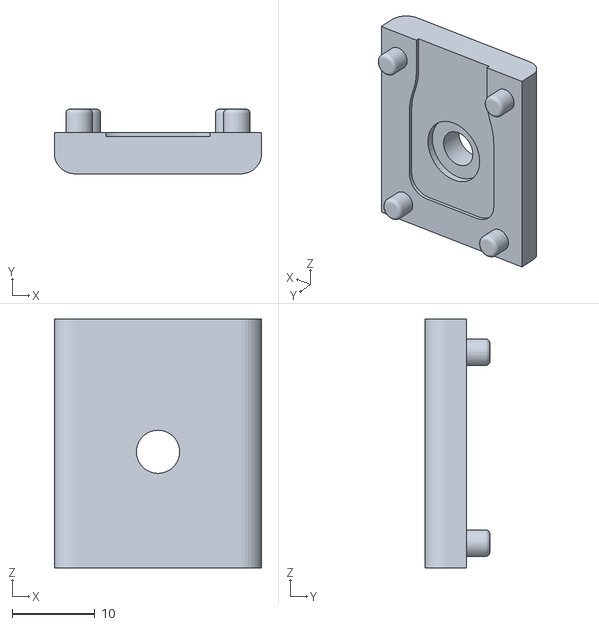
[picture p70: CAD file, 2022-05-07]
CAD/Flexiforce/Sensor holder upper 30mm.STL
25.0 x 7.80 x 30.0
