hannahstratfull/physiological-monitoring/CAD/Flexiforce/Button for 3d 2.STL

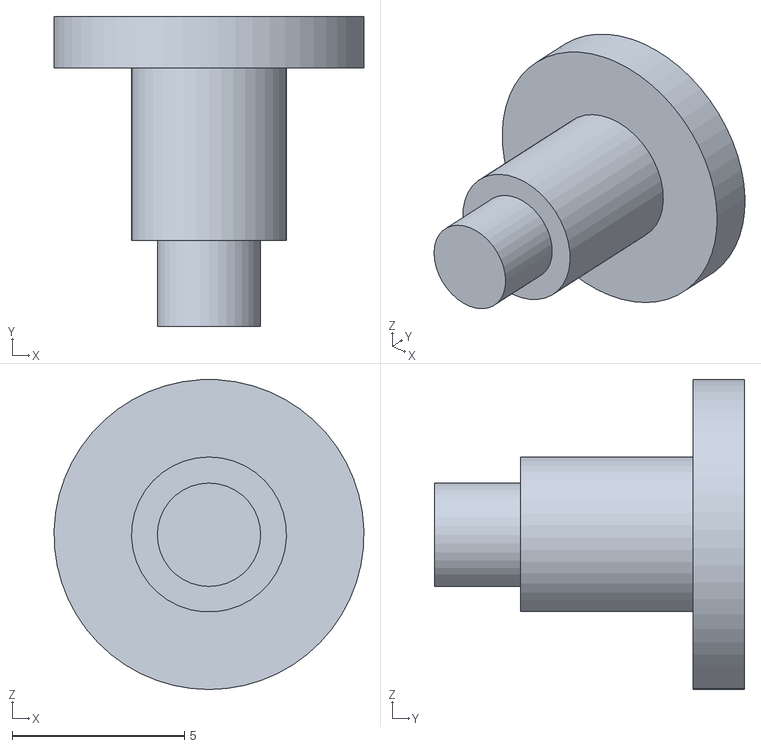
[picture p71: CAD file, 2022-05-07]
CAD/Flexiforce/Button for 3d 2.STL
9.00 x 9.00 x 9.00
