hannahstratfull/physiological-monitoring/CAD/Flexiforce/Flexiforce flex lid bat sec final mk3.STL

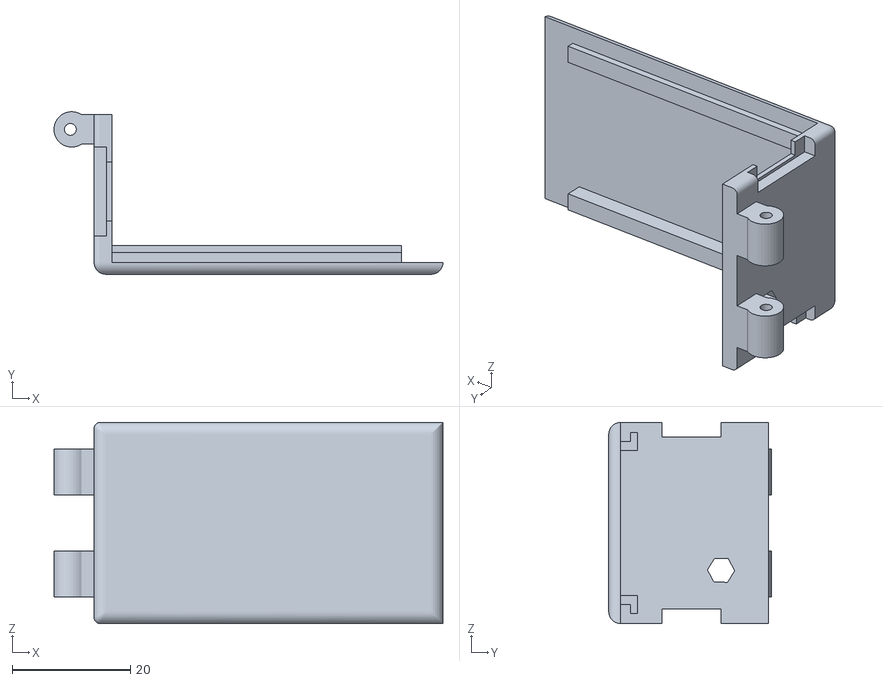
[picture p72: CAD file, 2022-05-07]
CAD/Flexiforce/Flexiforce flex lid bat sec final mk3.STL
65.8 x 27.5 x 34.0
