hannahstratfull/physiological-monitoring/CAD/Flexiforce/Felxiforce case with hoop - Flexiforce hoop-2.STL

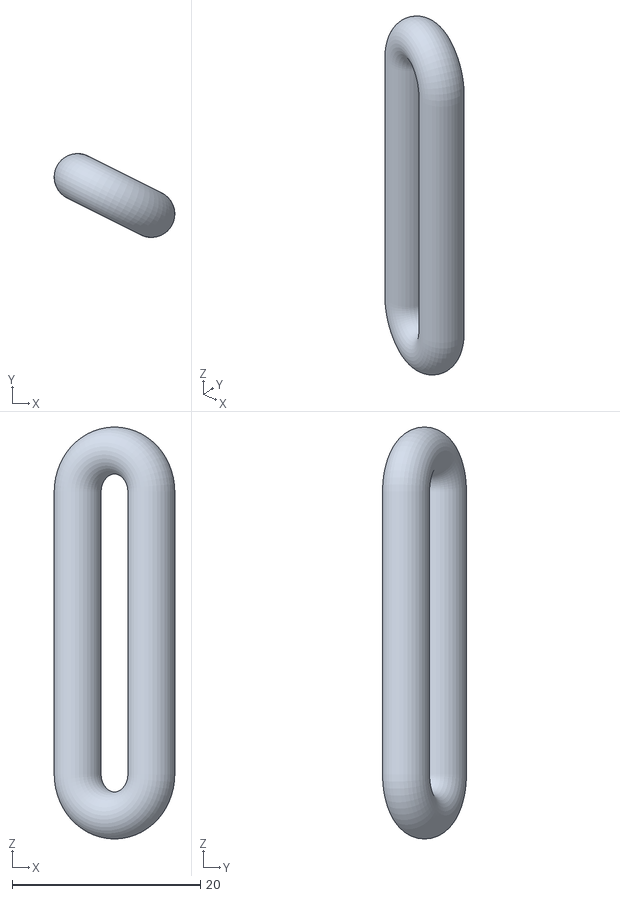
[picture p73: CAD file, 2022-05-07]
CAD/Flexiforce/Felxiforce case with hoop - Flexiforce hoop-2.STL
12.8 x 8.91 x 43.8
