hannahstratfull/physiological-monitoring/CAD/Flexiforce/Sensor holder lower for 3d print.STL

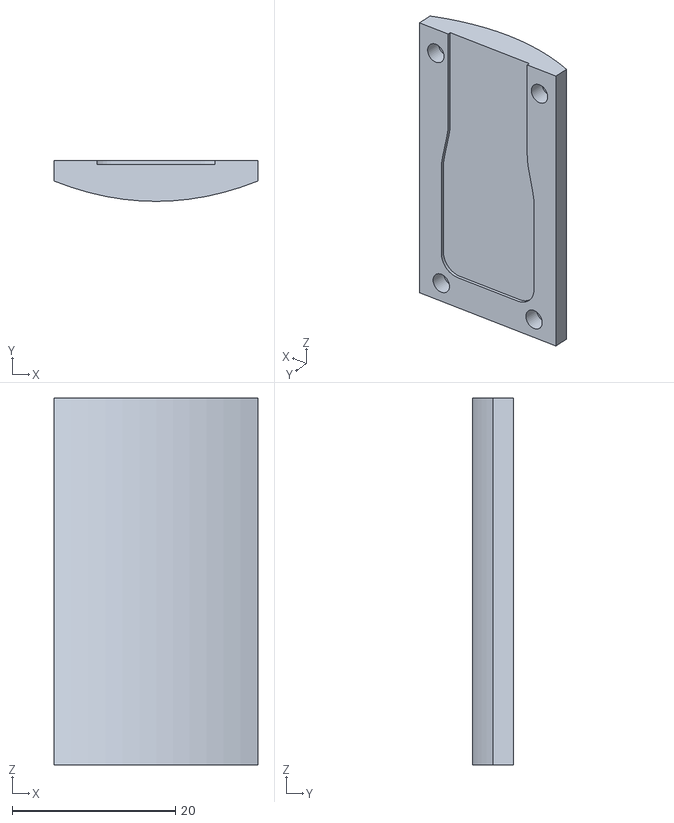
[picture p74: CAD file, 2022-05-07]
CAD/Flexiforce/Sensor holder lower for 3d print.STL
25.0 x 5.00 x 45.0
