hannahstratfull/physiological-monitoring/CAD/Flexiforce/Flexiforce hoop - half.STL

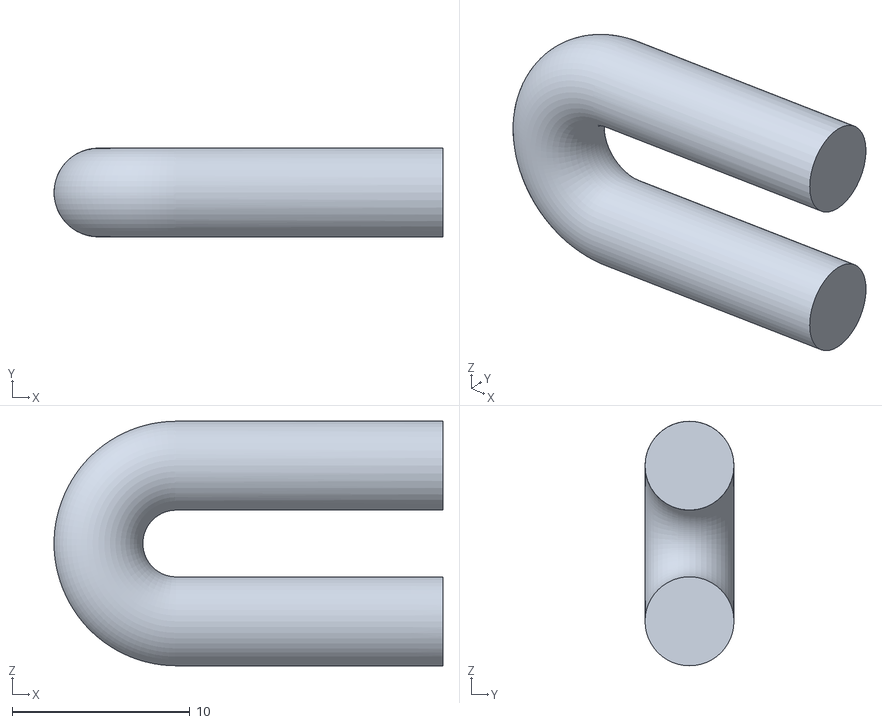
[picture p75: CAD file, 2022-05-07]
CAD/Flexiforce/Flexiforce hoop - half.STL
21.9 x 5.00 x 13.7
