hannahstratfull/physiological-monitoring/CAD/Flexiforce/hole plug v1 0.2mm wedge.STL

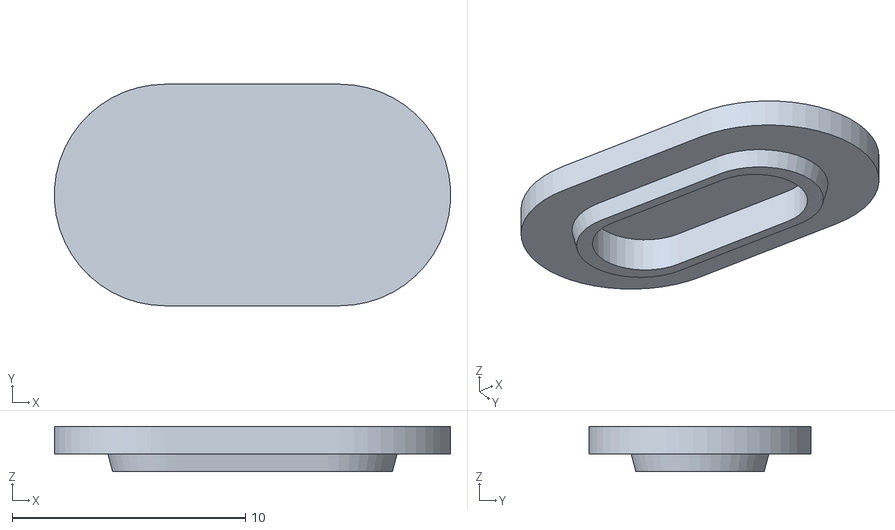
[picture p76: CAD file, 2022-05-07]
CAD/Flexiforce/hole plug v1 0.2mm wedge.STL
17.0 x 9.50 x 1.95
