hannahstratfull/physiological-monitoring/CAD/Flexiforce/Flexiforce flex lid bat sec MK1.SLDPRT

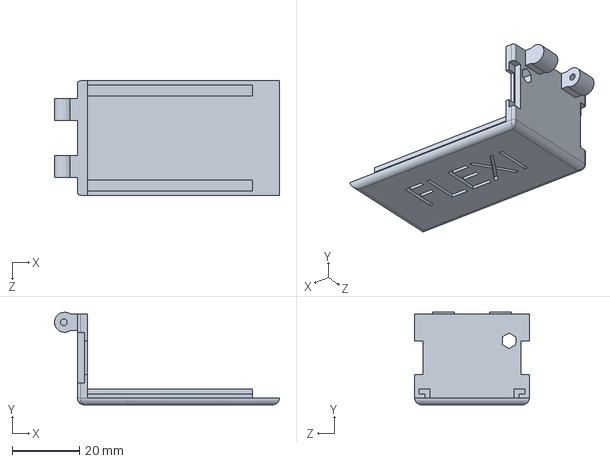
[picture p77: CAD file, 2022-05-07]
CAD/Flexiforce/Flexiforce flex lid bat sec MK1.SLDPRT
66.8 x 27.5 x 34.0 mm
