hannahstratfull/physiological-monitoring/CAD/Flexiforce/Felxiforce case with hoop mk2 - Flexiforce hoop-1.STL

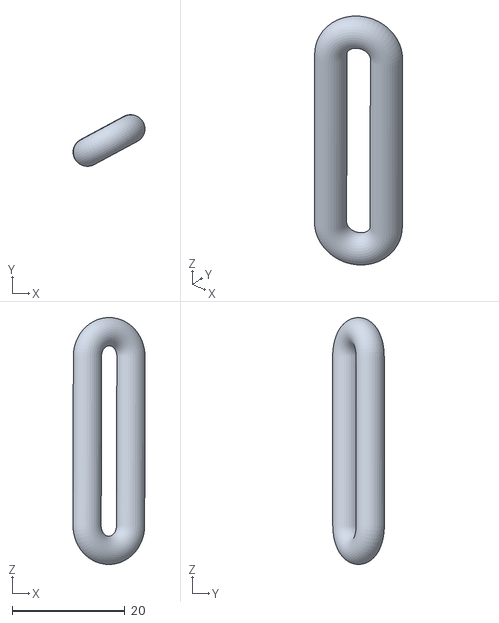
[picture p78: CAD file, 2022-05-07]
CAD/Flexiforce/Felxiforce case with hoop mk2 - Flexiforce hoop-1.STL
12.8 x 9.16 x 43.7
