hannahstratfull/physiological-monitoring/CAD/Flexiforce/Button for 3d print.STL

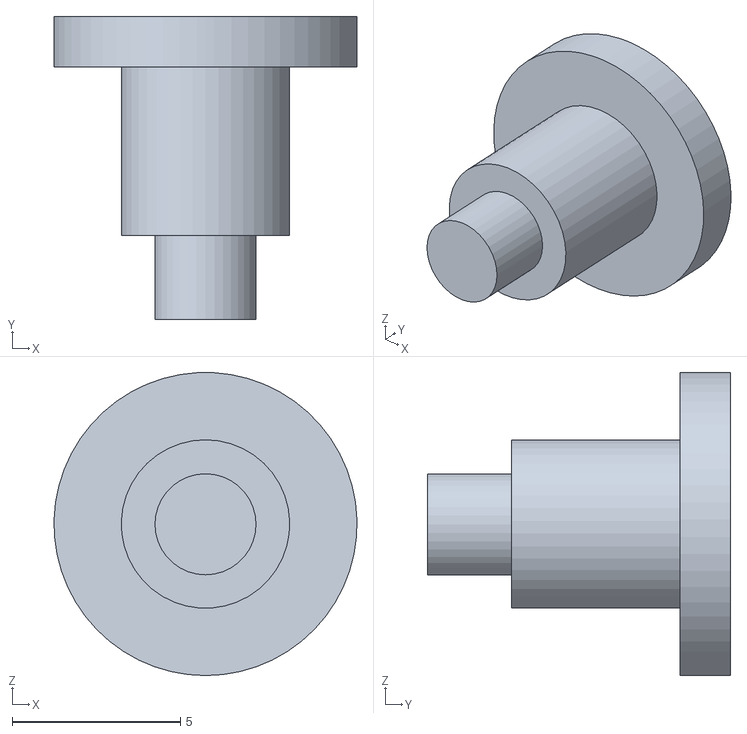
[picture p79: CAD file, 2022-05-07]
CAD/Flexiforce/Button for 3d print.STL
9.00 x 9.00 x 9.00
