hannahstratfull/physiological-monitoring/CAD/Flexiforce/Sensor compressive case 30mm.STL

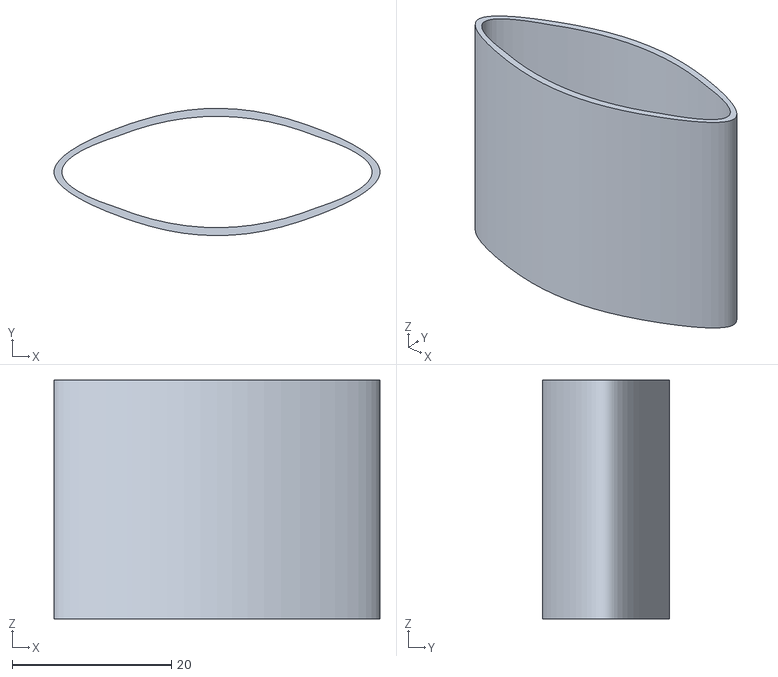
[picture p80: CAD file, 2022-05-07]
CAD/Flexiforce/Sensor compressive case 30mm.STL
41.0 x 16.0 x 30.0
